Norovl/Meteo_32x32_CO2_STM32/firmware/digits.ino

// ==================== матрицы цифр ====================


// размер цифр: (Шир + Выс * 8). x = (код % 8). y = (код - х) / 8 (размер шрифта)
uint8_t szFont[7] = { 42, 43, 59, 75, 60, 76, 34 };

// 10 цифр 2х4 пикселей
uint8_t digit24[10] = { 0b11111111, 0b01010101, 0b11011011, 0b11010111, 0b11110101, 0b11100111, 0b11101111, 0b11010101, 0b11001111, 0b11110111 };
// 10 цифр 2х5 пикселей + ":" (0)
int16_t digit25[11] = { 0b1111111111, 0b0101010101, 0b1101111011, 0b1101110111, 0b1111110101, 0b1110110111, 0b1110111111, 0b1101010101, 0b1111001111, 0b1111110111, 0b0001000100 };
// 10 цифр 3х5 пикселей + (11)"%", (12)":", (13)"+", (14)"-", (15)"↑", (16)"↓"  (1)
int16_t digit35[16] = { 0b111101101101111, 0b010010010010010, 0b111001111100111, 0b111001111001111, 0b101101111001001, 0b111100111001111, 0b111100111101111, 0b111001010010010,
                        0b111101111101111, 0b111101111001111, 0b100001010100001, 0b000010000010000, 0b000010111010000, 0b000000111000000, 0b010111010010010, 0b010010010111010 };
// 10 цифр 3х7 пикселей + (11)"%" (2)
uint32_t digit37[11] = { 0b111101101101101101111, 0b010010010010010010010, 0b111001001111100100111, 0b111001001111001001111, 0b101101101111001001001, 0b111100100111001001111,
                         0b111100100111101101111, 0b111001001010010010010, 0b111101101111101101111, 0b111101101111001001111, 0b000100001010100001000 };
// 10 цифр 3х9 пикселей (4)
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
  for (byte num = 0; num < (w * h); num++) {
    // жестко фиксируем высоту и ширину (32) - нет в шапке
    if ((x < 32) && (y < 32)) mSet(x + (num % w), y + (num / w), (symb & ((uint64_t)1 << ((w * h - 1) - num))) ? color : 0);
  }
}

// ----------Вывод буквы 3х5 (некоторые 4x5 и 5х5 при ext=true)----------
void symbSet(int8_t x, int8_t y, byte sym, int32_t color, boolean ext) {
  if ((ext) && ((sym == 148) || (sym == 150) || (sym == 156) || (sym == 164) || (sym == 168) || (sym == 169) || (sym == 171) || (sym == 174))) {  // 5x5
    switch (sym) {
      case 148:  //Д
        sym = 0;
        break;
      case 150:  //Ж
        sym = 1;
        break;
      case 156:  //М
        sym = 2;
        break;
      case 164:  //Ф
        sym = 3;
        break;
      case 168:  //Ш
        sym = 4;
        break;
      case 169:  //Щ
        sym = 5;
        break;
      case 171:  //Ы
        sym = 6;
        break;
      case 174:  //Ю
        sym = 7;
        break;
    }
    // 5x5
    symbSetx(x, y, symb55[sym], 5, 5, color);

  } else if ((ext) && ((sym == 152) || (sym == 153) || (sym == 170))) {  // 4х5
    switch (sym) {
      case 152:  //И
        sym = 0;
        break;
      case 153:  //Й
        sym = 1;
        break;
      case 170:  //Ъ
        sym = 2;
        break;
    }
    // 4x5
    symbSetx(x, y, symb45[sym], 4, 5, color);

  } else if (sym == 32) mSetFill(x, y, 0, 3, 5);                       //digSet35(x, y, 0, 0, 0, 0);              // пробел
  else if (sym == 37) symbSetx(x, y, 0b100001010100001, 3, 5, color);  //digSet35(x, y, 10, color, 10, 0);        // процент
  else if (sym == 46) symbSetx(x, y, 0b00001, 1, 5, color);            //digSet35(x - 1, y, 11, color, 11, 0);    // точка - смещаем на 1 пиксель влево
  else if (sym == 58) symbSetx(x, y, 0b01010, 1, 5, color);            //digSet35(x - 1, y, 11, color, 11, 0);    // двоеточие - смещаем на 1 пиксель влево
  else symbSetx(x, y, symb35[sym - 144], 3, 5, color);                 // 3x5
}

// ----------Вывод цифры w*h----------
void digSetwh(int8_t x, int8_t y, uint64_t dig, int32_t color, uint64_t digPrev, byte scr, byte w, byte h) {
  if (scr == 0) (digPrev = dig);
  if ((scr > h) || (dig == digPrev)) scr = h + 1;
  int32_t col = 0;

  // Проход по всем пикселям w*h
  for (byte num = 0; num < (w * h); num++) {

    byte colIdx = num % w;
    byte rowIdx = num / w;

    if ((h - scr) == rowIdx) col = 0;  // делаем пустую строку

    // Вывод пикселя старой цифры с учётом смещения scr
    if (rowIdx + scr < h) {
      if (digPrev & ((int64_t)1 << (w * h - 1 - (rowIdx + scr) * w - colIdx))) {
        col = color;
      } else {
        col = 0;
      }
    }

    // Вывод части новой цифры под старой
    if (rowIdx + scr >= (h + 1) && rowIdx + scr < (h * 2 + 1)) {
      if (dig & ((int64_t)1 << (w * h - 1 - (rowIdx + scr - (h + 1)) * w - colIdx))) {
        col = color;
      } else {
        col = 0;
      }
    }

    mSet(x + colIdx, y + rowIdx, col);
  }
}

// Вывод числа цифрами размером sz = 0 - 2х5; = 1 - 3х5; = 2 - 3х7; = 3 - 4х7; digits = количество цифр с отображением ведущих нулей, отрицательное - вместо ведущих нулей пробелы, 0 - без ведущих знаков
// digsPrev - предыдущее число для скролла, scroll - количество строк поднятия вверх старой цифры и отображения под ней новой, mbr - минимальная яркость канала (RGB) при наличии на нем цвета
void digPrintM(int8_t x, int8_t y, int digs, int32_t color, byte sz, byte digits, int digsPrev, byte scroll, uint8_t mbr) {
  // Serial.println(digs);
  uint8_t dig = 0;
  uint8_t digPrev = 0;
  if (scroll == 0) digsPrev = digs;
  for (byte d = 1; d <= abs(digits); d++) {  // Цикл по цифрам
    dig = abs(digs % 10);
    digPrev = abs(digsPrev % 10);  // предыдущее число для скролла
    switch (sz) {
      case 0:
        digSetwh(x + (abs(digits) - d) * 3, y, digit25[dig], color, digit25[digPrev], scroll, 2, 5);
        break;
      case 1:
        digSetwh(x + (abs(digits) - d) * 4, y, digit35[dig], color, digit35[digPrev], scroll, 3, 5);
        break;
      case 2:
        digSetwh(x + (abs(digits) - d) * 4, y, digit37[dig], color, digit37[digPrev], scroll, 3, 7);
        break;
      case 3:
        digSetwh(x + (abs(digits) - d) * 4, y, digit39[dig], color, digit39[digPrev], scroll, 3, 9);
        break;
      case 4:
        digSetwh(x + (abs(digits) - d) * 5, y, digit47[dig], color, digit47[digPrev], scroll, 4, 7);
        break;
      case 5:
        digSetwh(x + (abs(digits) - d) * 5, y, digit49[dig], color, digit49[digPrev], scroll, 4, 9);
        break;
      case 100:
        digSetwh(x + (abs(digits) - d) * 3, y, digit24[dig], color, digit24[digPrev], scroll, 2, 4);
        break;
    }
    digs = digs / 10;
    digsPrev = digsPrev / 10;
  }
}

// x, y, цифра, цвет, шрифт, кол-во отображаемых цифр, предыдущая цифра, скролл между предыдущей и текущей.
void digPrint(int8_t x, int8_t y, int digs, int32_t color, byte sz, byte digits, int digsPrev, byte scroll) {
  digPrintM(x, y, digs, color, sz, digits, digsPrev, scroll, 1);
}

// Вывод слова txt цветом color, размером 3х5 (при ext=true некоторые буквы 5х5)
void symPrint(int8_t x, int8_t y, const char* str, int32_t color, boolean ext) {
  byte plusx = 0;  // смещение координат Х для вывода следующей буквы
  //byte i = 0;
  while (*str > 0) {
    if (*str != 208) {  // если не второй код (юникод?) русской раскладки
      symbSet(x + plusx, y, *str, color, ext);
      plusx = plusx + 4;

      // если широкая буква и ext=true, то следующую смещаем на 1 или 2 позиции (И Й Ъ - на 1, Д Ж М Ф Ш Щ Ы Ю на 2)
      if ((ext) && (((*str) == 148) || ((*str) == 150) || ((*str) == 156) || ((*str) == 164) || ((*str) == 168) || ((*str) == 169) || ((*str) == 171) || ((*str) == 174))) plusx += 2;
      if ((ext) && (((*str) == 152) || ((*str) == 153) || ((*str) == 170))) plusx++;
    }
    str++;
  }
}
